MrChunckuee-Electronics/ROBOT-HCSR04_Project/Firmware/word_config.h

/* 
 * File:   word_config.h
 * Author: MrChunckuee
 *
 * Created on 20 de mayo de 2013, 09:42 PM
 */

#ifndef WORD_CONFIG_H
#define	WORD_CONFIG_H

// Configuracion del microcontrolador PIC18F1320
#pragma config OSC = INTIO2     //Uso de oscilador interno
#pragma config FSCM = OFF
#pragma config IESO = OFF
#pragma config PWRT = ON
#pragma config BOR = OFF
#pragma config WDT = OFF
#pragma config MCLRE = ON       //Master Clear activado
#pragma config STVR = ON
#pragma config LVP = OFF
#pragma config DEBUG = ON
#pragma config CP0 = OFF
#pragma config CP1 = OFF
#pragma config CPD = OFF
#pragma config WRT0 = OFF
#pragma config WRT1 = OFF
#pragma config WRTC = OFF
#pragma config WRTD = OFF
#pragma config EBTR0 = OFF
#pragma config EBTR1 = OFF
#pragma config EBTRB = OFF


#endif	/* WORD_CONFIG_H */
